LaheyKevin/Slimme_Baken_PoAB/Componenten/lichtmeting/temt6000/temtlichtmetingtest2/temtlichtmetingtest2.ino

int LIGHTSENSORPIN = A0;
//#define LIGHTSENSORPIN A1

void setup()
{
  pinMode(LIGHTSENSORPIN, INPUT);
  Serial.begin(9600);
}

void loop()
{
  float reading = analogRead(LIGHTSENSORPIN); //Read light level
  float square_ratio = reading / 1023.0; //Get percent of maximum value (1023)
  square_ratio = pow(square_ratio, 2.0);
  Serial.println(reading);
  delay(1000);
}
